AvailibleName/ceeo-LEGO-anything-sensor/python_lib/legoeducation/basic_device.py

"""
This module provides a helper class for interacting with the LEGO Education
device BLE RPC service.
"""

#!/usr/bin/env python

import threading
import inspect
import logging
from typing import Callable, Any, Dict
import time
import struct
from collections import deque
from math import log2
from concurrent.futures import Future

from .background_worker import Worker
from .rpc_message import *  # noqa: F403
from .rpc_message import device_notification_parser as _raw_device_notification_parser
from .color_map import _translate_notification_colors, _app_to_firmware, VALID_LEGO_COLOR, VALID_LEGO_COLOR_STRING_FORMAT


import atexit
import inspect
import re
from functools import wraps

# Format used for packing a single message id byte
MESSAGE_ID_FMT = '<B'

SERVICE_UUID = "0000FD02-0000-1000-8000-00805F9B34FB"
WRITE_UUID = "0000FD02-0001-1000-8000-00805F9B34FB"
NOTIFY_UUID = "0000FD02-0002-1000-8000-00805F9B34FB"

UINT8_MAX = 0xFF
UINT16_MAX = 0xFFFF
UINT32_MAX = 0xFFFFFFFF
INT8_MIN = -128
INT8_MAX = 127
INT16_MIN = -32768
INT16_MAX = 32767
INT32_MIN = -2147483648
INT32_MAX = 2147483647

DEVICE_NOTIFICATION_MIN_INTERVAL_MS = 15
DEVICE_NOTIFICATION_MAX_INTERVAL_MS = 1000
DEFAULT_DEVICE_NOTIFICATION_DELAY = 100

# Timeout for first notification after connect. 1.0 second chosen as a balance
# between device readiness (typical notification arrives in <200ms) and user
# experience (longer waits degrade perceived connection speed).
DEFAULT_FIRST_NOTIFICATION_TIMEOUT = 1.0

# Polling interval while waiting for BLE connection to be established
_CONNECT_POLL_INTERVAL_S = 0.05

# Conservative default fallback: ATT MTU(247) - ATT header(3) = 244 bytes.
# Actual packet size is negotiated with the device and loaded from info().
DEFAULT_MAX_PACKET_SIZE = 244

VALID_MOTOR_INDICES = {0, 1}
my_worker = Worker()


def _extract_docstring_section(doc, section_name):
    lines = doc.splitlines()
    normalized_target = section_name.strip().lower()
    section_start = _find_section_start(lines, normalized_target)
    if section_start is None:
        return None

    section_start = _skip_blank_lines(lines, section_start)
    block_lines = _collect_section_lines(lines[section_start:])
    return _dedent_block_lines(block_lines)


def _find_section_start(lines, normalized_target):
    for idx, line in enumerate(lines):
        if _line_section_title(line) == normalized_target:
            return idx + 1
    return None


def _skip_blank_lines(lines, start_index):
    while start_index < len(lines) and not lines[start_index].strip():
        start_index += 1
    return start_index


def _collect_section_lines(lines):
    block_lines = []
    for line in lines:
        if line and line == line.lstrip() and _line_section_title(line) is not None:
            break
        block_lines.append(line)
    return block_lines


def _dedent_block_lines(block_lines):
    block = "\n".join(block_lines)
    lines = block.splitlines()
    # drop leading/trailing empty lines
    while lines and not lines[0].strip():
        lines.pop(0)
    while lines and not lines[-1].strip():
        lines.pop()
    # remove common leading whitespace
    if not lines:
        return None
    indent = min((len(line) - len(line.lstrip())) for line in lines if line.strip())
    cleaned = "\n".join(line[indent:] for line in lines)
    return cleaned or None


def _line_section_title(line):
    stripped = line.strip()
    if not stripped:
        return None

    if stripped.startswith("#"):
        stripped = stripped.lstrip("#").strip()
        if not stripped:
            return None
        return stripped.rstrip(":").strip().lower()

    match = re.match(r"^(?P<title>[A-Za-z][A-Za-z0-9 _-]*)::?\s*$", stripped)
    if match:
        return match.group("title").strip().lower()
    return None


def get_simple_example(func):
    doc = inspect.getdoc(func) or ""
    return _extract_docstring_section(doc, "simple example")


def get_more_example(func):
    doc = inspect.getdoc(func) or ""
    return _extract_docstring_section(doc, "more examples")

def enforce_usage(func):
    """
    Catches TypeError from wrong argument usage and shows
    the correct call from the docstring.
    """
    @wraps(func)
    def wrapper(*args, **kwargs):
        try:
            return func(*args, **kwargs)  # run the actual function normally
        except TypeError as e:
            example_usage = get_simple_example(func)
            more_example_usage = get_more_example(func)
            msg = f"Incorrect call to {func.__name__}()."
            if example_usage:
                indented = "\n".join("    " + line for line in example_usage.splitlines())
                msg += f"\r\nSimple Example:\n\n{indented}\n"
            if more_example_usage:
                indented_more = "\n".join("    " + line for line in more_example_usage.splitlines())
                msg += f"\nMore Examples:\n\n{indented_more}\n"
            msg += f"\nOriginal error: {e}"
            raise TypeError(msg) from None
    return wrapper


class _BatchContext:
    """Context manager returned by _BasicDevice.batch()."""

    __slots__ = ('_device', '_blocking')

    def __init__(self, device, blocking):
        self._device = device
        self._blocking = blocking

    def __enter__(self):
        self._device.begin_batch()
        return self._device

    def __exit__(self, exc_type, exc_val, exc_tb):
        if exc_type is not None:
            # Exception occurred inside the block — clean up without sending
            self._device._reset_batch_state()
            return False  # re-raise the exception
        try:
            self._device.end_batch(blocking=self._blocking)
        except Exception:
            # end_batch failed (e.g. BLE error) — clean up and propagate
            self._device._reset_batch_state()
            raise
        return False


class VersionMismatchError(Exception):
    """Raised when the device's RPC version does not match the client's expected version."""


class _BasicDevice:
    """Internal base class for LEGO Education device communication.

    Not part of the public API — users should instantiate SingleMotor,
    DoubleMotor, Controller, or ColorSensor instead.
    """

    def __init__(self, device_name="any", device_mac="any", card_color=-1, card_serial=-1, callback=None):
        self._Background_thread_start()
        atexit.register(self._Background_thread_end)
        self.service_uuid = SERVICE_UUID
        self.device_name = device_name
        self.device_mac = device_mac
        self.card_color = card_color
        self.card_serial = self._normalize_card_serial(card_serial)
        self.device = None
        self.connected = False
        self.scanning = False
        self.my_worker = my_worker
        self.device_list = []
        self._last_scan_filters = None
        # Map of response_id -> deque of asyncio.Future objects
        # We use a deque so we can support multiple outstanding responses for the
        # same response ID (FIFO). This is required for MOTOR_*_RESULT messages
        # which can run in parallel.
        self._pending_responses = {}    # Dictionary[int, Deque[asyncio.Future]]
        self.logger = logging.getLogger(__name__)
        self._notification_callback = callback

        self.info_device = InfoDeviceNotification(0, USB_POWER_STATE_USB_NOT_CONNECTED)
        self.scanned_card = CardNotification(-1, 0)
        self.button = ButtonStateNotification(BUTTON_STATE_RELEASED)
        self.version_firmware = ()
        self.version_rpc = ()
        self.version_bootloader = ()

        # Response ids that can have multiple outstanding requests and need
        # differentiation by the first byte in the response payload (motor id)
        self._multi_by_motor = {
            MOTOR_RUN_FOR_DEGREES_RESULT,
            MOTOR_RUN_FOR_TIME_RESULT,
            MOTOR_RUN_TO_ABSOLUTE_POSITION_RESULT,
            MOTOR_RUN_TO_RELATIVE_POSITION_RESULT,
        }

        # Signal set when first DEVICE_NOTIFICATION is processed
        # used by connect() to wait for sensor values to be initialized.
        self._first_notification_ready = threading.Event()

        # Batch mode state (guarded by _batch_lock for thread safety)
        self._batch_lock = threading.Lock()
        self._batch_mode = False
        self._batch_buffer = []  # List of serialized command bytes
        self._batch_size = 0  # Running total of buffered bytes
        self._batch_motors = set()  # Track motors with pending action commands

    def _validate_int(self, value, name):
        if isinstance(value, bool) or not isinstance(value, int):
            raise TypeError(f"{name} must be an integer")
        return value

    def _validate_bool(self, value, name):
        if not isinstance(value, bool):
            raise TypeError(f"{name} must be a boolean")
        return value
    
    def _validate_range(self, value, *, name=None, minimum=None, maximum=None):
        if minimum is not None and value < minimum:
            raise ValueError(f"{name} must be >= {minimum}")
        if maximum is not None and value > maximum:
            raise ValueError(f"{name} must be <= {maximum}")
        return value

    def _validate_int_range(self, value, name, *, minimum=None, maximum=None):
        number = self._validate_int(value, name)
        number = self._validate_range(number, name=name, minimum=minimum, maximum=maximum)
        return number
    
    def _validate_int_float_range(self, value, name, *, minimum=None, maximum=None):
        if isinstance(value, bool) or not isinstance(value, (int, float)):
            raise TypeError(f"{name} must be an int or float")
        number = self._validate_range(value, name=name, minimum=minimum, maximum=maximum)
        return int(number+0.5)  # Round to nearest integer

    def _validate_enum(self, value, name, valid_values, *, valid_str_fmt=None):
        number = self._validate_int(value, name)
        if number not in valid_values:
            raise ValueError(f"Enum type: {name} must be one of {valid_str_fmt if valid_str_fmt else sorted(valid_values)}")
        return number

    def _validate_callable(self, callback, name):
        if callback is not None and (not callable(callback) or inspect.isclass(callback)):
            raise TypeError(f"{name} must be callable function or None")

    def _validate_timeout(self, value, name):
        if isinstance(value, bool) or not isinstance(value, (int, float)):
            raise TypeError(f"{name} must be an int or float")
        if value < 0:
            raise ValueError(f"{name} must be positive")
        return float(value)

    def _validate_thread(self, name):
        worker_thread = self.my_worker.ble_thread
        if worker_thread is not None and threading.current_thread() is worker_thread:
            raise RuntimeError(f"Function '{name}' cannot be called from the callback thread")

    def _reset_batch_state_locked(self):
        """Reset batch mode state. Caller must hold _batch_lock."""
        self._batch_mode = False
        self._batch_buffer = []
        self._batch_size = 0
        self._batch_motors = set()

    def _reset_batch_state(self):
        """Reset batch mode state under lock."""
        with self._batch_lock:
            self._reset_batch_state_locked()

    @staticmethod
    def _normalize_card_serial(value):
        """Return a zero-padded 4-digit string for a valid card serial
        (0-9999).

        Sentinel/unset values (None or -1) are returned as -1 unchanged.
        Values that cannot be parsed or are out of range are also returned as -1.
        """
        if value is None or value == -1:
            return -1
        try:
            parsed = int(value)
            if 0 <= parsed <= 9999:
                return "{:04d}".format(parsed)
            return -1
        except (TypeError, ValueError):
            return -1

    @staticmethod
    def _coerce_filter_value(value):
        try:
            return -1 if value is None else int(value)
        except (TypeError, ValueError):
            return -1

    def _compose_filters(self, device_name=None, device_mac=None, card_color=None, card_serial=None):
        return {
            'device_name': device_name,  # Only set when user explicitly provides it
            'device_mac': device_mac if device_mac is not None else self.device_mac,
            'card_color': self._coerce_filter_value(self.card_color if card_color is None else card_color),
            'card_serial': self._coerce_filter_value(self.card_serial if card_serial is None else card_serial),
            'product_id': getattr(self, 'product_id', None),
        }
    def _Background_thread_start(self):
        """Start the background worker thread that handles BLE I/O.
        Call before using any hardware APIs."""
        my_worker.start_thread()

    def _Background_thread_end(self):
        """Stop the background worker thread and release BLE resources.
        Safe to call when finished interacting with hardware."""
        my_worker.close_thread()

    def _scan_callback(self, devices):
        # Callback from worker thread after scan completes; store results.
        self.device_list = devices or []
        self.scanning = False

    def _ask(self, topic, message = None, message2 = None, message3 = None, message4 = None):
        worker_thread = self.my_worker.ble_thread
        if worker_thread is not None and threading.current_thread() is worker_thread and topic != 'send': # 'send' is allowed here, since a special check is done in _send_commands():
            raise RuntimeError("This function cannot be called from the callback thread")
        payload = {}
        payload['topic'] = topic
        payload['msg'] = message
        payload['msg2'] = message2
        payload['msg3'] = message3
        payload['msg4'] = message4
        self.my_worker.put_request(payload)

    async def _handle_device_notification(self, payload: bytes):
        """Parse and handle device notification messages."""
        # Manual parsing
        if len(payload) >= 2:
            device_data_length = struct.unpack('<H', payload[:2])[0]
            device_data = payload[2:2 + device_data_length] if len(payload) >= 2 + device_data_length else payload[2:]
        else:
            device_data_length = len(payload)
            device_data = payload
        # Create device notification object
        device_notification = DeviceNotification(
            deviceDataByteLength=device_data_length,
            deviceData=device_data
            )

        try:
            parsed_items = _raw_device_notification_parser(device_notification)
            _translate_notification_colors(parsed_items)

            for parsed_item in parsed_items:
                if isinstance(parsed_item, InfoDeviceNotification):
                    self.info_device = parsed_item
                if isinstance(parsed_item, CardNotification):
                    self.scanned_card = parsed_item
                if isinstance(parsed_item, ButtonStateNotification):
                    self.button = parsed_item
                if isinstance(parsed_item, MotorNotification) and hasattr(self, 'motor'):
                    if isinstance(self.motor, list):  # DoubleMotor
                        self.motor[int(log2(parsed_item.motorBitMask))] = parsed_item
                    else:  # SingleMotor
                        self.motor = parsed_item
                if isinstance(parsed_item, ImuGestureNotification) and hasattr(self, 'imu_gesture'):
                    self.imu_gesture = parsed_item
                if isinstance(parsed_item, ImuDeviceNotification) and hasattr(self, 'imu_device'):
                    self.imu_device = parsed_item
                if isinstance(parsed_item, ControllerNotification) and hasattr(self, 'sensor'):
                    self.sensor = parsed_item
                if isinstance(parsed_item, ColorSensorNotification) and hasattr(self, 'sensor'):
                    self.sensor = parsed_item

            # Signal that first notification has been received and parsed
            self._first_notification_ready.set()

        except Exception:
            self.logger.exception(
                "Error parsing device notification; raw payload %s",
                payload.hex(),
            )
            # Still signal readiness even on parse error; notification arrived
            self._first_notification_ready.set()

        if self._notification_callback:
            # Handle both sync and async callbacks
            if inspect.iscoroutinefunction(self._notification_callback):
                await self._notification_callback(device_notification)
            else:
                self._notification_callback(device_notification)

    async def _device_callback(self, characteristic, data):
        """Internal notification handler that parses and routes messages."""
        try:
            # print(f"Callback data: {data.hex()}")
            if len(data) < 1:
                return
            # Parse message ID and payload
            message_id = data[0]
            payload = data[1:] if len(data) > 1 else b''

            # Check if this is a response we're waiting for. _pending_responses
            # holds a deque of futures for each response id (or composite key
            # when multiplexed by motor id). We pop the oldest future (FIFO)
            # and set its result so multiple identical response message ids
            # can be handled in parallel.
            # If the message id is multiplexed by motor, use the first byte of
            # the payload as the motor id to select the correct pending future.
            lookup_key = message_id
            if message_id in self._multi_by_motor and len(payload) >= 1:
                motor_id = payload[0]
                lookup_key = (message_id, motor_id)

            # if message_id != DEVICE_NOTIFICATION:
            #     print("Response from device with key:", lookup_key)

            if lookup_key in self._pending_responses:
                dq = self._pending_responses.get(lookup_key)
                if dq:
                    try:
                        future = dq.popleft()
                    except IndexError:
                        future = None
                    # Clean up empty deque
                    if not dq:
                        self._pending_responses.pop(lookup_key, None)
                else:
                    future = None
                if future is not None and not future.cancelled():
                    # print("Setting result for future, payload:", payload.hex())
                    future.set_result(payload)
                return

            # Handle device notifications
            if message_id == DEVICE_NOTIFICATION:
                await self._handle_device_notification(payload)

            # else:
            #     print(f"Received unexpected message ID: {message_id}")

        except Exception:
            self.logger.exception("Notification handling error")

    def _connect_callback(self, success):
        if success:
            self.connected = True
        else:
            self.logger.error("Could not establish BLE connection")

    def _disconnect_callback(self):
        self.connected = False
        self.logger.info("Disconnected from BLE device")

    def _send_commands(self, *messages , blocking=True):
        """Low-level utility: send one or more serialized command frames
        and optionally wait for responses.
        Users normally call higher-level APIs instead of this directly."""
        if not self.connected:
            self.logger.error("Attempted to send command without an active connection")
            return None

        # Batch mode: buffer commands instead of sending.
        # Size accounting: serialized messages are concatenated directly into a
        # single BLE write (no per-message framing or length prefix on the wire),
        # so summing len(msg) accurately tracks the payload size against
        # maxPacketSize.
        if self._batch_mode:
            with self._batch_lock:
                for msg in messages:
                    new_size = self._batch_size + len(msg)
                    max_size = getattr(self, 'maxPacketSize', DEFAULT_MAX_PACKET_SIZE)
                    if new_size > max_size:
                        raise RuntimeError(
                            f"Batch full ({new_size} > {max_size} bytes). "
                            "Call end_batch() before adding more commands."
                        )
                    self._batch_buffer.append(msg)
                    self._batch_size += len(msg)
            return None

        # blocking_check should tell us if just one or more of blocking is true
        blocking_check = any(blocking) if isinstance(blocking, list) else blocking
        worker_thread = self.my_worker.ble_thread
        if worker_thread is not None and threading.current_thread() is worker_thread and blocking_check:
            raise RuntimeError("This function cannot be called from callback thread with 'blocking=True'")

        futures = []
        message_bytes = bytes()
        wait_plan = []   # subset of futures to actually wait for
        for i, msg in enumerate(messages):

            message_bytes = message_bytes + msg
            # Determine expected response message ID
            response_id = msg[0] + 1
            # print(f"Sending message ID {msg[0]}, expecting response ID {response_id}")
            # Set up response waiting. Use a deque to allow multiple outstanding
            # futures for the same response_id (FIFO).

            future = Future()
            futures.append(future)

            should_block = (blocking if isinstance(blocking, bool)
                else (i < len(blocking) and blocking[i]))
            if should_block:
                wait_plan.append(future)
            # Determine lookup key: for motor-multiplexed responses we can use the
            # first byte of the payload (if present) to create a composite key so
            # responses are matched per-motor. If payload doesn't contain motor id
            # yet, fall back to the general response_id key.
            lookup_key = response_id
            if response_id in self._multi_by_motor:
                motor_id = msg[1]
                lookup_key = (response_id, motor_id)
            dq = self._pending_responses.get(lookup_key)
            if dq is None:
                dq = deque()
                self._pending_responses[lookup_key] = dq
            # print("lookup_key", lookup_key)
            dq.append(future)
        # print(len(wait_plan))
        # print(message_bytes)

        try:
            # Send command
            self._ask('send', self.device, message_bytes)
            # Block on requested futures until they complete. 
            for f in wait_plan:
                f.result()

            if not wait_plan:
                return None
            if len(wait_plan) == 1:
                return wait_plan[0].result()

            return [f.result() for f in wait_plan]

        except Exception as e:
            self._pending_responses.pop(response_id, None)
            raise e

    # Public API functions (shared across tech elements)
    @enforce_usage
    def begin_batch(self):
        """Start batching commands into a single BLE packet. When batch
        mode is active, motor commands are queued instead of being sent
        immediately. Call `end_batch()` to send all queued commands in a
        single packet. This ensures they all start nearly simultaneously.
        Note: If a previous batch was never ended, it is automatically
        discarded and a warning is logged.
        
        Simple Example:
        
            # Double Motor: configure Double Motor and start both motors together
            doublemotor.begin_batch()
            doublemotor.motor_run(motor=le.MOTOR_LEFT, speed=50)
            doublemotor.motor_run(motor=le.MOTOR_RIGHT, speed=10)
            doublemotor.end_batch() # start together
        """
        with self._batch_lock:
            if self._batch_mode:
                n = len(self._batch_buffer)
                self.logger.warning(
                    "Previous batch was never ended — discarding %d buffered command(s)", n
                )
            self._batch_mode = True
            self._batch_buffer = []
            self._batch_size = 0
            self._batch_motors = set()

    @enforce_usage
    def end_batch(self, blocking=True):
        """Sends all batched commands in a single packet. To use
        effectively, use `begin_batch()` to create a queue of motor
        commands and call `end_batch()` to start all queued commands
        nearly simultaneously.
        
        Parameters:
            blocking: Wait for the command(s) to be completed before continuing.
        
        Simple Example:
        
            # Double Motor: configure Double Motor and start both motors together
            doublemotor.begin_batch()
            doublemotor.motor_run(motor=le.MOTOR_LEFT, speed=50)
            doublemotor.motor_run(motor=le.MOTOR_RIGHT, speed=10)
            doublemotor.end_batch() # start together
        """
        self._validate_blocking(blocking)
        with self._batch_lock:
            if not self._batch_mode:
                raise RuntimeError("No batch in progress. Call begin_batch() first.")

            if not self._batch_buffer:
                self._reset_batch_state_locked()
                self.logger.warning("end_batch() called with no commands in batch")
                return None

            messages = self._batch_buffer
            self._batch_mode = False

        try:
            # All commands in batch share the same blocking flag. This means
            # end_batch(blocking=True) waits for every response, which is safe
            # but may be slower than necessary for fire-and-forget commands like
            # motor_set_speed. A future optimisation could track per-command
            # blocking intent, but the current approach is simpler and correct.
            blocking_plan = [blocking] * len(messages)
            return self._send_commands(*messages, blocking=blocking_plan)
        except Exception:
            # Restore batch state so user can retry or inspect
            with self._batch_lock:
                self._batch_mode = True
            raise
        finally:
            with self._batch_lock:
                if not self._batch_mode:
                    self._reset_batch_state_locked()

    @enforce_usage
    def batch(self, blocking=True):
        """Context manager for batch mode operations. This block
        automatically calls `begin_batch()` on entry and `end_batch()` on
        exit. If an error occurs inside the block, it ensures batch mode
        is properly closed.
        
        Parameters:
            blocking: Wait for the command(s) to be completed before continuing.
        
        Simple Example:
        
            # Double Motor: configure Double Motor and start both motors together
            with doublemotor.batch():
                doublemotor.motor_run(motor=le.MOTOR_LEFT, speed=50)
                doublemotor.motor_run(motor=le.MOTOR_RIGHT, speed=10)
        """
        self._validate_blocking(blocking)
        return _BatchContext(self, blocking)

    @enforce_usage
    def cancel_batch(self):
        """Cancel the current batch without sending any commands. Returns
        the number of commands that were discarded.
        
        Simple Example:
        
            # Double Motor: configure Double Motor but cancel batch
            doublemotor.begin_batch()
            doublemotor.motor_run(motor=le.MOTOR_LEFT, speed=50)
            doublemotor.motor_run(motor=le.MOTOR_RIGHT, speed=10)
            doublemotor.cancel_batch()

        More Examples:

            # Double Motor: configure Double Motor but cancel batch and print number of commands discarded.
            doublemotor.begin_batch()
            doublemotor.motor_run(motor=le.MOTOR_LEFT, speed=50)
            doublemotor.motor_run(motor=le.MOTOR_RIGHT, speed=10)
            num = doublemotor.cancel_batch()
            print(f'Cancelled batch. {num} commands canceled.')
        """
        with self._batch_lock:
            if not self._batch_mode:
                raise RuntimeError("No batch in progress. Call begin_batch() first.")
            n = len(self._batch_buffer)
            self._reset_batch_state_locked()
        return n

    @enforce_usage
    def search(self, timeout = 5, device_name=None, device_mac=None, card_color=None, card_serial=None):
        """Use Bluetooth to scan for nearby hardware that matches the
        listed criteria.
        
        Parameters:
            timeout: Duration of scan in seconds.
            device_name: Filter for hardware by name contents.
            device_mac: Filter for hardware by MAC address contents.
            card_color: Filter for hardware by Connection Card of a specific
                color using a LEGO Color constant.
            card_serial: Filter for hardware by Connection Card of a specific
                serial number. Use a string (e.g., "0049") for serial
                numbers with leading zeros.
        
        Simple Example:
        
            # Color Sensor: Search for all available Color Sensors.
            colorsensor = le.ColorSensor()
            sensorlist = colorsensor.search()

        More Examples:
        
            # Filter for Controllers by Connection Card of color red
            controller = le.Controller()
            sensorlist = controller.search(card_color=le.LEGO_COLOR_RED)
            # Print each Controller found
            if (sensorlist):
                for i in range(len(sensorlist)):
                    print(sensorlist[i])
        """
        if self._batch_mode:
            raise RuntimeError("search() cannot be called inside a batch")
        # Prevent calling from callback thread
        self._validate_thread("search")

        timeout_value = self._validate_timeout(timeout, "timeout")
        filters = self._compose_filters(device_name, device_mac, card_color, card_serial)

        # Persist any provided filters to instance state so subsequent
        # calls can reuse them when caller passes None.
        if device_name is not None:
            self.device_name = device_name
        if device_mac is not None:
            self.device_mac = device_mac
        if card_color is not None:
            self.card_color = self._coerce_filter_value(card_color)
        if card_serial is not None:
            self.card_serial = self._normalize_card_serial(card_serial)

        # Perform the scan inline (formerly in scan()). Results arrive via _scan_callback.
        try:
            self.scanning = True
            self._ask('scan', timeout_value, self._scan_callback, filters)
            while self.scanning:
                time.sleep(0.05)
            self._last_scan_filters = filters
        except KeyboardInterrupt:
            # Reset scanning state and shut down the BLE worker thread so the
            # process can exit cleanly on Ctrl+C.
            self.scanning = False
            self.logger.info("Scan interrupted by user")
            self._Background_thread_end()
            raise
        except Exception:
            self.logger.exception("Scan request failed")
            return None

        if not self.device_list:
            parts = []
            if filters['device_name']:
                parts.append(f"name contains '{filters['device_name']}'")
            if filters['device_mac'] != 'any':
                parts.append(f"MAC contains '{filters['device_mac']}'")
            if filters['card_color'] != -1:
                parts.append(f"Card color {filters['card_color']}")
            if filters['card_serial'] != -1:
                normalized_card_serial = self._normalize_card_serial(filters['card_serial'])
                card_serial_text = normalized_card_serial if normalized_card_serial != -1 else filters['card_serial']
                parts.append(f"Card serial {card_serial_text}")
            self.logger.warning(
                "Could not find device matching %s",
                ", ".join(parts) if parts else "any filters",
            )
            return None

        return self.device_list

    @enforce_usage
    def connect(self, device=None, *, device_name=None, device_mac=None, card_color=None, card_serial=None, device_notification_delay = DEFAULT_DEVICE_NOTIFICATION_DELAY):
        """Connect to hardware. This function will use Bluetooth to scan
        and connect to the first hardware found based on any filters
        specified.
        
        Parameters:
            device: A device entry returned from `search()`. When `None`
                (default), a scan is performed automatically.
            device_name: Filter for hardware by name contents.
            device_mac: Filter for hardware by MAC address contents.
            card_color: Filter for hardware by a Connection Card of a
                specific color using a LEGO Color constant.
            card_serial: Filter for hardware by a Connection Card of a
                specific serial number. Use a string (e.g., "0049") for
                serials with leading zeros.
            device_notification_delay: Duration in milliseconds between
                automatic device notifications. When this value is greater
                than 0, the command waits for the first notification before
                returning. Must be 0 or between 15 and 1000.
        
        Simple Example:
        
            # Single Motor: Scan and connect to the first Single Motor found.
            singlemotor = le.SingleMotor()
            singlemotor.connect()
            
            # Double Motor: Scan and connect to the first Double Motor found.
            doublemotor = le.DoubleMotor()
            doublemotor.connect()

        More Examples:
        
            # Controller: Connect to a Controller indicated by the specified Connection Card.
            controller = le.Controller()
            controller.connect(card_color=le.LEGO_COLOR_RED, card_serial="1234")
        """
        if self._batch_mode:
            raise RuntimeError("connect() cannot be called inside a batch")
        # Prevent calling from callback thread
        self._validate_thread("connect")
        device_notification_delay = self._validate_int_float_range(
            device_notification_delay, "device_notification_delay", minimum=0, maximum=UINT16_MAX
        )
        if device_notification_delay != 0 and (
            device_notification_delay < DEVICE_NOTIFICATION_MIN_INTERVAL_MS
            or device_notification_delay > DEVICE_NOTIFICATION_MAX_INTERVAL_MS
        ):
            raise ValueError(
                f"device_notification_delay must be 0 (off) or between "
                f"{DEVICE_NOTIFICATION_MIN_INTERVAL_MS} and {DEVICE_NOTIFICATION_MAX_INTERVAL_MS} ms. "
                f"Got {device_notification_delay}. Use 0 to disable notifications, or a value in the "
                f"range [{DEVICE_NOTIFICATION_MIN_INTERVAL_MS}, {DEVICE_NOTIFICATION_MAX_INTERVAL_MS}]."
            )
        if device is None:
            found_device = self.search(timeout=0, device_name=device_name, device_mac=device_mac, card_color=card_color, card_serial=card_serial)
            if not found_device:
                return
            device = found_device[0]

        # Clear readiness signal for new connection
        self._first_notification_ready.clear()

        self.device = device
        self.connected = False
        try:
            self._ask('connect', device, self._device_callback, self._connect_callback, self._disconnect_callback)
            while not self.connected:
                time.sleep(_CONNECT_POLL_INTERVAL_S)

            response = self.info()

            self.version_firmware = (response.firmwareMajor, response.firmwareMinor, response.firmwareBuild)
            self.version_rpc = (response.rpcMajor, response.rpcMinor, response.rpcBuild)
            self.version_bootloader = (response.bootloaderMajor, response.bootloaderMinor, response.bootloaderBuild)
            self.maxPacketSize = response.maxPacketSize
            self.productGroupDevice = response.productGroupDevice

            if self.version_rpc != RPC_VERSION:
                self.connected = False
                self._ask("disconnect", self.device)
                if self.version_rpc > RPC_VERSION:
                    msg = (
                        "Your LEGO Education Python package needs updating.\n"
                        "Please run: pip install --upgrade legoeducation\n"
                        f"(device RPC version={self.version_rpc}, Python package RPC Version={RPC_VERSION})"
                    )
                else:
                    msg = (
                        "Your LEGO Education hardware needs a firmware update.\n"
                        "Please go to https://code.legoeducation.com/ and connect and update your hardware.\n"
                        f"(device RPC version={self.version_rpc}, Python package RPC Version={RPC_VERSION})"
                    )
                self.logger.warning(msg)
                raise VersionMismatchError(msg)

            if device_notification_delay > 0:
                self.device_notification_request(device_notification_delay)
                if not self._wait_for_first_notification(timeout=DEFAULT_FIRST_NOTIFICATION_TIMEOUT):
                    self.logger.warning(
                        "Timed out waiting for first device notification; "
                        "sensor values may still be uninitialized (nan)"
                    )
        except KeyboardInterrupt:
            # Ctrl+C can arrive during the polling loop, info(), or
            # notification setup — all are covered by this handler.
            self.connected = False
            self.logger.info("Connection interrupted by user")
            self._Background_thread_end()
            raise

    def _wait_for_first_notification(self, timeout: float) -> bool:
        """Wait for the first DEVICE_NOTIFICATION to be processed.
        
        Parameters:
            timeout: Maximum time in seconds to wait.
            
        Returns:
            True if notification was received within timeout, False otherwise.
        """
        return self._first_notification_ready.wait(timeout=timeout)

    @enforce_usage
    def disconnect(self):
        """Disconnect from the hardware. This resets the hardware back to
        Bluetooth broadcast mode.
        
        Simple Example:
        
            # Single Motor: Disconnect from the Single Motor.
            singlemotor.disconnect()
        """
        if self._batch_mode:
            raise RuntimeError("disconnect() cannot be called inside a batch")
        self._validate_thread("disconnect")
        # If device is None we still want to trigger a shutdown of any remaining connections
        if self.device is not None:
            self._ask('disconnect', self.device)
        else:
            # Fallback: ask worker to close all (handles partial init or previous disconnect)
            self._ask('close_all')

    @enforce_usage
    def set_notification_callback(self, callback: Callable[[Dict[str, Any]], Any]):
        """Register a callback function to handle hardware notifications.
        This method sets a callback function that will be invoked whenever
        the hardware sends sensor updates.
        
        Parameters:
            callback: A function that takes one argument
                (the notification object).
        
        Simple Example:
        
            # Single Motor: set a notification callback
            singlemotor.set_notification_callback(notification_callback)

        More Examples:
        
            # Define a function for handling Single Motor notifications
            def notification_callback(data):
                parsed_items = le.device_notification_parser(data)
                for parsed_item in parsed_items:
                    if isinstance(parsed_item, le.MotorNotification):
                        print(f"Single Motor position: {parsed_item.position}")
            # Set Single Motor notification callback
            singlemotor.set_notification_callback(notification_callback)
        """
        self._validate_callable(callback, "callback")
        self._notification_callback = callback

    @enforce_usage
    def info(self):
        """Returns technical information about the hardware.
        
        Simple Example:
        
            # Single Motor: Get technical information about the Single Motor
            info = singlemotor.info()

        More Examples:
        
            # Iterate through and print all technical information about the the Color Sensor
            for key, value in vars(colorsensor.info()).items():
                if (type(value) is int):
                    print(key, value)
        """
        instance = InfoRequest()
        msg = instance.Serialize()
        response = self._send_commands(msg, blocking=True)
        if response is None:
            return None

        return InfoResponse.Deserialize(response)

    @enforce_usage
    def device_uuid(self):
        """Get the Universally Unique Identifier (UUID) of the hardware.
        The UUID is linked to the hardware and does not change even if
        the device is reset or updated.
        
        Simple Example:
        
            # Single Motor: Print the UUID of a Single Motor.
            response = singlemotor.device_uuid()
            print(response.uuid.hex()) # print byte array as hex
        """
        instance = DeviceUuidRequest()
        msg = instance.Serialize()
        response = self._send_commands(msg, blocking=True)
        if response is None:
            return None

        return DeviceUuidResponse.Deserialize(response)

    @enforce_usage
    def program_flow_notification(self, action: int, *, blocking: bool = True):
        """Tell the hardware that a program has started or stopped. This
        resets many device settings depending on the chosen action.
        
        Parameters:
            action: Specify the type of program action using a Program Action
                constant.
            blocking: Wait for the command to be completed before continuing.
        
        Simple Example:
        
            # Single Motor: Mark the program as started.
            singlemotor.program_flow_notification(le.PROGRAM_ACTION_START)

        More Examples:
        
            # Mark the Single Motor program as stopped.
            singlemotor.program_flow_notification(le.PROGRAM_ACTION_STOP)
        """
        self._validate_enum(action, "action", VALID_PROGRAM_ACTION, valid_str_fmt=VALID_PROGRAM_ACTION_STRING_FORMAT)
        self._validate_bool(blocking, "blocking")
        instance = ProgramFlowNotification(action)
        msg = instance.Serialize()
        self._send_commands(msg, blocking=blocking)
        return

    @enforce_usage
    def device_notification_request(self, delay_ms: int, *, blocking: bool = True):
        """Set how often the hardware sends automatic notifications. The
        contents of the notification vary based on the type of hardware,
        and can include button presses, sensor values and other state
        changes reported by the hardware.
        
        Parameters:
            delay_ms: Duration in milliseconds between notifications.
                Must be 0 (to turn off notifications) or between 15 and 1000.
            blocking: Wait for the command to be completed before continuing.
        
        Simple Example:
        
            # Single Motor: Set duration between notifications to 50 milliseconds.
            singlemotor.device_notification_request(50)

        More Examples:
        
            # Turn off the automatic notifications on the Single Motor
            singlemotor.device_notification_request(0)
        """
        delay_ms = self._validate_int_float_range(delay_ms, "delay_ms", minimum=0, maximum=UINT16_MAX)
        if delay_ms != 0 and (delay_ms < DEVICE_NOTIFICATION_MIN_INTERVAL_MS or delay_ms > DEVICE_NOTIFICATION_MAX_INTERVAL_MS):
            raise ValueError(
                f"delay_ms must be 0 (off) or between "
                f"{DEVICE_NOTIFICATION_MIN_INTERVAL_MS} and {DEVICE_NOTIFICATION_MAX_INTERVAL_MS} ms. "
                f"Got {delay_ms}. Use 0 to disable notifications, or a value in the "
                f"range [{DEVICE_NOTIFICATION_MIN_INTERVAL_MS}, {DEVICE_NOTIFICATION_MAX_INTERVAL_MS}]."
            )
        self._validate_bool(blocking, "blocking")
        instance = DeviceNotificationRequest(delay_ms)
        msg = instance.Serialize()
        response = self._send_commands(msg, blocking=blocking)
        if response is None:
            return None
        
        return DeviceNotificationResponse.Deserialize(response)

    @enforce_usage
    def light_color(self, color: int, *, pattern: int = 0, intensity: int = 100, blocking: bool = True):
        """Set the button light color and blink pattern on the hardware.
        
        Parameters:
            color: Set the light color using a LEGO Color constant.
            pattern: Set the light behavior using a Light Pattern (Button on
                Hardware) constant.
            intensity: Set the brightness of the light as a percentage,
                ranging from 0% to 100% (default is 100).
            blocking: Wait for the command to be completed before continuing.
        
        Simple Example:
        
            # Single Motor: Set the button light to the color red on the Single Motor.
            singlemotor.light_color(le.LEGO_COLOR_RED)

        More Examples:
        
            # Set the light color on the Single Motor to blue and blink pattern to "breathe"
            singlemotor.light_color(le.LEGO_COLOR_BLUE, pattern=le.LIGHT_PATTERN_BREATHE)
            
            # Set the light color on the Single Motor to blue at 50% intensity
            singlemotor.light_color(le.LEGO_COLOR_BLUE, intensity=50)
            
            # Set the light color on the Single Motor to green with a "breathe" blink pattern and 75% intensity
            singlemotor.light_color(le.LEGO_COLOR_GREEN, pattern=le.LIGHT_PATTERN_BREATHE, intensity=75)
        """
        self._validate_enum(color, "color", VALID_LEGO_COLOR, valid_str_fmt=VALID_LEGO_COLOR_STRING_FORMAT)
        self._validate_enum(pattern, "pattern", VALID_LIGHT_PATTERN, valid_str_fmt=VALID_LIGHT_PATTERN_STRING_FORMAT)
        intensity = self._validate_int_float_range(intensity, "intensity", minimum=0, maximum=100)
        self._validate_bool(blocking, "blocking")
        fw_color = _app_to_firmware(color)
        instance = LightColorCommand(fw_color, pattern, intensity)
        msg = instance.Serialize()
        response = self._send_commands(msg, blocking=blocking)
        if response is None:
            return None

        return LightColorResult.Deserialize(response)

    @staticmethod
    def _create_beep_command(pattern, frequency, count):
        """Create a PlayBeepCommand, converting user-facing count to the
        value sent to firmware.

        The firmware field represents repeats after the first play,
        so we subtract 1 from the caller's count.
        """
        return PlayBeepCommand(pattern, frequency, count - 1)

    @enforce_usage
    def beep(self, pattern: int = SOUND_PATTERN_BEEP_SINGLE, *, frequency: int = 440, count: int = 1, blocking: bool = True):
        """Play a beep sound pattern on the hardware.
        
        Parameters:
            pattern: Specify the beep sound pattern to be played on the
                hardware using a Sound Pattern (Hardware Beep) constant.
            frequency: Set the frequency of the beep sound in hertz. Default
                is 440 Hz.
            count: Determine how many times the beep pattern should be
                repeated. Default is 1 (once).
            blocking: Wait for the command to be completed before continuing.
        
        Simple Example:
        
            # Single Motor: play a beep
            singlemotor.beep()

        More Examples:

            # Play a high "beep double" sound pattern on a Single Motor.
            singlemotor.beep(pattern=le.SOUND_PATTERN_BEEP_DOUBLE, frequency=880)

            # Play a low beep three times on a Color Sensor.
            colorsensor.beep(frequency=220, count=3)
        """
        self._validate_enum(pattern, "pattern", VALID_SOUND_PATTERN)
        frequency = self._validate_int_float_range(frequency, "frequency", minimum=0, maximum=2700)
        self._validate_int_range(count, "count", minimum=1, maximum=255)
        self._validate_bool(blocking, "blocking")
        instance = self._create_beep_command(pattern, frequency, count)
        msg = instance.Serialize()
        response = self._send_commands(msg, blocking=blocking)
        if response is None:
            return None

        return PlayBeepResult.Deserialize(response)

    @enforce_usage
    def stop_beep(self, *, blocking: bool = True):
        """Stop any ongoing beep sound from the hardware.
        
        Parameters:
            blocking: Wait for the command to be completed before continuing.
        
        Simple Example:
        
            # Single Motor: Stop any ongoing beep sounds from the Single Motor.
            singlemotor.stop_beep()

        More Examples:

            # Start playing many low beeps on a Color Sensor.
            colorsensor.beep(frequency=220, count=10, blocking=False)
            time.sleep(3)
            colorsensor.stop_beep() # stop beep sounds after three seconds
        """
        self._validate_bool(blocking, "blocking")
        instance = StopSoundCommand()
        msg = instance.Serialize()
        response = self._send_commands(msg, blocking=blocking)
        if response is None:
            return None

        return StopSoundResult.Deserialize(response)
