AvailibleName/ceeo-LEGO-anything-sensor/python_lib/legoeducation/basic_ble.py

import asyncio
import logging
import threading
from typing import Callable, Optional

try:  # Make bleak optional; raise only when used.
    from bleak import BleakClient, BleakScanner
except Exception:  # pragma: no cover - bleak may be absent
    BleakClient = BleakScanner = None  # type: ignore

from .ble_transport import BLETransport
from .color_map import _firmware_to_app

SERVICE_UUID = "0000FD02-0000-1000-8000-00805F9B34FB"
SERVICE_UUID_LOWER = SERVICE_UUID.lower()
WRITE_UUID   = "0000FD02-0001-1000-8000-00805F9B34FB"   # RX - for sending data TO the hub
NOTIFY_UUID  = "0000FD02-0002-1000-8000-00805F9B34FB"   # TX - for receiving data FROM the hub
LEGO_COMPANY_ID = 0x0397  # LEGO company ID for BLE manufacturer data

class BasicBLE(BLETransport):
    """Bleak-based BLE transport implementing BLETransport.

    This remains backwards compatible for existing imports while enabling
    end-user override via ble_transport.register_transport()."""

    def __init__(self, *, shutdown_callback: Optional[Callable[[], None]] = None):
        super().__init__(shutdown_callback)
        self.device_list = []
        self.client_list = {}
        self.client = None
        self._filters = self._normalize_filters(None)
        # Thread-safe cancellation flag.  Set from the main thread via
        # request_cancel(); polled from the BLE thread inside scan/connect
        # loops at ~0.1 s intervals. Cleared by the worker loop before each
        # new request dispatch (see background_worker.py).
        self._cancel_event = threading.Event()

    def request_cancel(self):
        """Request cancellation of any in-progress scan/connect operation.

        Thread-safe: can be called from any thread (typically the main thread
        via Worker.cancel_current_operation)."""
        self._cancel_event.set()

    def reset_cancel(self):
        """Clear cancellation request state prior to a new operation.

        Called by the worker loop right before dispatching a request so that
        stale cancel state from a previous operation does not leak."""
        self._cancel_event.clear()

    def _normalize_filters(self, raw_filters):
        if isinstance(raw_filters, str):
            raw_filters = {'device_name': raw_filters}

        raw_filters = raw_filters or {}

        def _clean(value, *invalid):
            if value is None:
                return None
            value = str(value).strip()
            return None if value.lower() in invalid else value

        def _coerce(value):
            try:
                return -1 if value is None else int(value)
            except (TypeError, ValueError):
                return -1

        return {
            'device_name': _clean(raw_filters.get('device_name'), '', 'any'),
            'device_mac': _clean(raw_filters.get('device_mac'), '', 'any'),
            'card_color': _coerce(raw_filters.get('card_color')),
            'card_serial': _coerce(raw_filters.get('card_serial')),
            'product_id': raw_filters.get('product_id'),
        }

    @staticmethod
    def _normalize_card_serial(value):
        if value is None or value == -1:
            return -1
        try:
            parsed = int(value)
            if 0 <= parsed <= 9999:
                return "{:04d}".format(parsed)
            return -1
        except (TypeError, ValueError):
            return -1

    def _describe_filters(self):
        parts = []
        if self._filters['device_name']:
            parts.append(f"name contains '{self._filters['device_name']}'")
        if self._filters['device_mac']:
            parts.append(f"MAC contains '{self._filters['device_mac']}'")
        if self._filters['card_color'] != -1:
            parts.append(f"Card color {self._filters['card_color']}")
        if self._filters['card_serial'] != -1:
            normalized_card_serial = self._normalize_card_serial(self._filters['card_serial'])
            card_serial_text = normalized_card_serial if normalized_card_serial != -1 else self._filters['card_serial']
            parts.append(f"Card serial {card_serial_text}")
        if self._filters.get('product_id') is not None:
            parts.append(f"product ID {self._filters['product_id']}")
        return ", ".join(parts) if parts else "no filters"

    @staticmethod
    def _extract_manufacturer_info(advertisement):
        """Extract product_id, card_color, and card_serial from LEGO manufacturer data.

        LEGO devices always send a fixed-size manufacturer data payload
        (6 bytes after the 2-byte company ID is stripped by bleak).
        If the data is missing or not the expected length, the device is ignored.

        Returns:
            Tuple of (product_id, card_color, card_serial). All values are None
            if the manufacturer data is missing or has unexpected length.
        """
        try:
            data = getattr(advertisement, 'manufacturer_data', None) or {}
            lego_data = data.get(LEGO_COMPANY_ID)
            if lego_data is None or len(lego_data) < 5:
                return None, None, None
            # Product ID = (product_group << 8) | product_device (big-endian)
            # Firmware sends [group, device].
            product_id = (lego_data[0] << 8) | lego_data[1]
            card_color = _firmware_to_app(lego_data[2])
            card_serial = lego_data[3] | (lego_data[4] << 8)
            return product_id, card_color, card_serial
        except (AttributeError, IndexError, TypeError):
            return None, None, None

    def _matches_filters(self, device, advertisement):
        # Only match connectable devices (AC1)
        # On WinRT, connectable may be None for scan-response packets;
        # treat None the same as True (unknown ≠ non-connectable).
        connectable = getattr(advertisement, 'connectable', True)
        if connectable is not None and not connectable:
            return False

        # Service UUID check — safety net alongside BleakScanner filter (AC2)
        uuids = [uuid.lower() for uuid in getattr(advertisement, "service_uuids", [])]
        if SERVICE_UUID_LOWER not in uuids:
            return False

        filters = self._filters

        # Extract manufacturer data once for product_id + card filters
        product_id, card_color, card_serial = self._extract_manufacturer_info(advertisement)

        # Match by product_id from manufacturer data ADV package (AC3)
        if filters.get('product_id') is not None:
            if product_id is None or product_id != filters['product_id']:
                return False

        # Name filter — only when user explicitly passes device_name=
        if filters['device_name']:
            if not device.name or filters['device_name'].lower() not in device.name.lower():
                return False

        if filters['device_mac']:
            if not device.address or filters['device_mac'].lower() not in device.address.lower():
                return False

        if filters['card_color'] != -1 or filters['card_serial'] != -1:
            if filters['card_color'] != -1:
                if card_color is None or card_color != filters['card_color']:
                    return False
            if filters['card_serial'] != -1:
                if card_serial is None or card_serial != filters['card_serial']:
                    return False

        return True

    def on_scan(self, device, adv):
        if self._matches_filters(device, adv):
            if not any(d.address == device.address for d in self.device_list):
                self.device_list.append(device)

    async def scan_devices(self, timeout, filters = None):
        """Scan for BLE devices. Supports cancellation via _cancel_event.

        Returns None when cancelled (both scan modes) so callers can
        distinguish "nothing found" from "interrupted"."""
        try:
            self._filters = self._normalize_filters(filters)
            # Special semantics: timeout == 0 means "first match" mode with a 10s upper bound.
            if timeout == 0:
                self.logger.info("Scanning (first match, max 10s) for %s", self._describe_filters())
                self.device_list = []
                scanner = BleakScanner(detection_callback=self.on_scan, service_uuids=[SERVICE_UUID])
                await scanner.start()
                try:
                    loop = asyncio.get_running_loop()
                    end = loop.time() + 10.0
                    while loop.time() < end:
                        if self._cancel_event.is_set():
                            break
                        # Break as soon as we have at least one matching device
                        if self.device_list:
                            break
                        await asyncio.sleep(0.1)
                finally:
                    await scanner.stop()
                # Return a single-element list (consistent return type) or None when not found
                if self._cancel_event.is_set():
                    return None
                return self.device_list if self.device_list else None

            # Normal multi-scan behavior for timeout > 0
            self.logger.info("Scanning for %s over %s sec", self._describe_filters(), timeout)
            self.device_list = []
            scanner = BleakScanner(detection_callback=self.on_scan, service_uuids=[SERVICE_UUID])
            await scanner.start()
            try:
                for _ in range(100):
                    if self._cancel_event.is_set():
                        break
                    await asyncio.sleep(timeout/100)
            finally:
                await scanner.stop()
            if self._cancel_event.is_set():
                return None
            return self.device_list
        except Exception:
            self.logger.exception("BLE scan error")
            return None

    async def device_disconnect(self, device):  # explicit device disconnect requested by worker
        """Explicitly disconnect a device, tolerating partially initialized state.
        This does NOT route through on_disconnect() directly; instead it performs
        the transport-level shutdown then invokes _cleanup_device() and possibly
        shutdown_all()."""
        if device is None:
            self.logger.debug("device_disconnect called with None device")
            return
        entry = self.client_list.get(getattr(device, 'address', None))
        if not entry:
            self.logger.debug("device_disconnect: no client entry for %s", getattr(device, 'address', 'unknown'))
            return
        client = entry.get('client')
        from_device = entry.get('from_device')
        try:
            if client and from_device:
                try:
                    await client.stop_notify(from_device)
                except Exception:
                    self.logger.debug("stop_notify failed or not active for %s", getattr(device, 'address', 'unknown'))
            if client:
                await client.disconnect()
        except Exception:
            self.logger.exception("Error during device_disconnect for %s", getattr(device, 'address', 'unknown'))
        self._cleanup_device(client)

    def _cleanup_device(self, client):
        """Remove a single client's bookkeeping, invoke its user-level disconnect callback.
        Safe to call multiple times; races are tolerated with try/except."""
        if client is None or not self.client_list:
            return
        matching_addr = next((addr for addr, info in self.client_list.items() if info.get('client') == client), None)
        if matching_addr is None:
            return
        try:
            info = self.client_list.get(matching_addr)
            if info is None:
                return
            device_name = getattr(info.get('device'), 'name', matching_addr)
            self.logger.info("Connection to %s lost", device_name)
            dis_callback = info.get('disconnect_callback')
            if dis_callback:
                try:
                    dis_callback()
                except Exception:
                    self.logger.debug("Disconnect callback raised for %s", device_name)
            self.client_list.pop(matching_addr, None)
        except Exception:
            self.logger.exception("BLE disconnect cleanup error for %s", matching_addr)

    def shutdown_all(self):
        """Global shutdown: disconnect every remaining client (best-effort) and invoke shutdown callback."""
        if not self.client_list:
            # still invoke callback in case caller expects it even with nothing left
            if self.shutdown_callback:
                self.shutdown_callback()
            return

        # Collect async disconnect coroutines so we can await them properly.
        disconnect_coros = []

        for addr, info in list(self.client_list.items()):
            client = info.get('client')
            # Invoke per-device disconnect callback first (mirrors _cleanup_device semantics)
            dis_callback = info.get('disconnect_callback')
            if dis_callback:
                try:
                    dis_callback()
                except Exception:
                    self.logger.debug("Disconnect callback raised during global shutdown for %s", addr)
            if client:
                try:
                    # Support both sync and async disconnect implementations.
                    res = client.disconnect()
                    if asyncio.iscoroutine(res):
                        disconnect_coros.append(res)
                except Exception:
                    self.logger.debug("Error disconnecting client %s during global shutdown", addr)

        # Actually await all disconnect coroutines so the BLE disconnect
        # packet is sent before the event loop shuts down. Without this the
        # remote device only discovers the link loss after the supervision
        # timeout (~24 s).
        if disconnect_coros:
            try:
                loop = asyncio.get_running_loop()
                # We are inside an async context (worker_loop). Schedule all
                # disconnects as a single task so they can complete before the
                # loop exits. Store the task so the worker loop's final await
                # can pick it up.
                self._pending_disconnect_task = asyncio.ensure_future(
                    asyncio.gather(*disconnect_coros, return_exceptions=True),
                    loop=loop,
                )
            except RuntimeError:
                # No running loop; best-effort synchronous run.
                try:
                    asyncio.run(asyncio.gather(*disconnect_coros, return_exceptions=True))
                except Exception:
                    self.logger.debug("Could not await BLE disconnects during shutdown", exc_info=True)

        self.client_list.clear()
        self.logger.info("All BLE connections closed; shutting down")
        if self.shutdown_callback:
            self.shutdown_callback()

    def on_disconnect(self, client):
        """Bleak disconnected_callback entry point.
        Cleans up per-client state but does not shut down the worker."""
        if client is None:
            return
        self._cleanup_device(client)

    async def connect(self, device, callback, disconnect_callback):
        self.logger.info("Connecting to %s (%s)", getattr(device, "name", "unknown"), getattr(device, "address", "unknown"))
        try:
            if BleakClient is None:
                raise RuntimeError("bleak not installed; cannot connect with BasicBLE")
            client = BleakClient(device, disconnected_callback=self.on_disconnect)
            # Early exit if cancel was already requested before we start.
            if self._cancel_event.is_set():
                return False
            # Make client.connect() interruptible by polling _cancel_event
            # every 0.1 s — same pattern used in scan_devices(). Without this,
            # client.connect() can block for 5-30 s with no way to abort.
            connect_task = asyncio.ensure_future(client.connect())
            try:
                while not connect_task.done():
                    if self._cancel_event.is_set():
                        connect_task.cancel()
                        try:
                            await connect_task
                        except asyncio.CancelledError:
                            pass  # Expected when we cancel the task
                        except Exception:
                            self.logger.debug("Error awaiting cancelled connect task", exc_info=True)
                        # Best-effort cleanup: disconnect if the underlying
                        # transport managed to establish a link before we
                        # cancelled the task.
                        try:
                            if client.is_connected:
                                await client.disconnect()
                        except Exception:
                            self.logger.debug("Failed to disconnect client during cancel cleanup", exc_info=True)
                        return False
                    await asyncio.sleep(0.1)
                # Propagate any exception that occurred inside client.connect()
                connect_task.result()
            except asyncio.CancelledError:
                return False

            # Final cancel check: covers the tiny window between the task
            # completing and the service-setup code below.
            if self._cancel_event.is_set():
                try:
                    if client.is_connected:
                        await client.disconnect()
                except Exception:
                    self.logger.debug("Failed to disconnect client after connect cancellation", exc_info=True)
                return False

            success = client.is_connected
            if success:
                service = client.services.get_service(SERVICE_UUID)
                to_device = service.get_characteristic(WRITE_UUID)
                from_device = service.get_characteristic(NOTIFY_UUID)
                self.client_list[device.address] = {
                    'client': client,
                    'device': device,
                    'to_device': to_device,
                    'from_device': from_device,
                    'disconnect_callback': disconnect_callback,
                }
                if callback:
                    await client.start_notify(from_device, callback)
                self.logger.info("Connected to %s (%s)", getattr(device, "name", "unknown"), getattr(device, "address", "unknown"))
            else:
                self.logger.error("Unable to connect to %s", getattr(device, "name", "unknown"))
            return success
        except Exception:
            self.logger.exception("BLE connect error")
            return False

    async def send(self, device, message: bytes):
        entry = self.client_list.get(device.address)
        if not entry:
            self.logger.error("Attempted send with unknown device %s", getattr(device, 'address', 'unknown'))
            return
        await entry['client'].write_gatt_char(entry['to_device'], message, response=False)
